OpenNextion/OpenNextion-SKU-ONX3248G035/Example Programs/ESP-IDF/05_wifi_test/README_en.md

# ESP32-S3 Wi-Fi Test Example

## Overview

This example demonstrates Wi-Fi scanning, connection, and status display on the ONX3248G035 development board (ESP32-S3). The UI is built with LVGL and the Wi-Fi logic is provided by the `wifi_manager` component.

## Purchase Links

- Product: [Open Nextion 3.5" Genius Series ESP32-S3 LCD Touchscreen Development Board](https://itead.cc/product/open-nextion-3-5-genius-series-esp32-s3-lcd-touchscreen-development-board/)

## Features

- **Wi-Fi scan**: scan nearby APs.
- **Wi-Fi connect**: select an SSID and connect (common WPA/WPA2).
- **Status UI**: show connection state and errors.

## Hardware Requirements

- **MCU**: ESP32-S3 Development Board
- **LCD**: 3.5-inch ST7796U SPI TFT LCD (320x480)
- **Touch**: CST826 I2C capacitive touch controller
- **IO Expander**: PCF8574 I2C IO expander

## Pin Connections (aligned with code)

| Function | ESP32-S3 Pin | Description |
| :--- | :--- | :--- |
| **I2C** | | |
| I2C SCL | GPIO_NUM_7 | I2C Clock |
| I2C SDA | GPIO_NUM_8 | I2C Data |
| **SPI (LCD)** | | |
| SPI SCLK | GPIO_NUM_5 | SPI Clock |
| SPI MOSI | GPIO_NUM_1 | SPI Data |
| LCD DC | GPIO_NUM_3 | LCD Data/Command |
| LCD CS | GPIO_NUM_2 | LCD Chip Select |
| **Other** | | |
| LCD BL | GPIO_NUM_6 | Backlight (PWM) |
| LCD RST | - | Controlled via PCF8574 |

## How to Use

1. **Connect hardware**: LCD + touch + board.
2. **Build and flash**.
3. **Provision Wi-Fi**: scan and select SSID on the screen, then enter password.

## Build and Flash

1. Set target:
   ```bash
   idf.py set-target esp32s3
   ```
2. Build:
   ```bash
   idf.py build
   ```
3. Flash and monitor:
   ```bash
   idf.py -p <PORT> flash monitor
   ```

## Notes

- Only 2.4 GHz Wi-Fi is supported on ESP32-S3.
- Use `menuconfig` to adjust Wi-Fi settings if needed.
