OpenNextion/OpenNextion-SKU-ONX3248G035/Example Programs/ESP-Arduino/02_music_test/build_opt.h

-DLV_CONF_SKIP
-DLV_USE_DEMO_MUSIC=1
-DLV_DEMO_MUSIC_SQUARE=0
-DLV_DEMO_MUSIC_LANDSCAPE=0
-DLV_DEMO_MUSIC_ROUND=0
-DLV_DEMO_MUSIC_LARGE=0
-DDEMO_MUSIC_AUTO_PLAY=0
-DLV_FONT_MONTSERRAT_16=1
-DLV_FONT_MONTSERRAT_22=1
-DLV_FONT_MONTSERRAT_32=1
