OpenNextion/OpenNextion-SKU-ONX3248G035/Example Programs/ESP-IDF/09_outofbox_demo/components/board/include/board_wifi.h

#ifndef  _BOARD_INCLUDE_BOARD_WIFI_H_
#define  _BOARD_INCLUDE_BOARD_WIFI_H_

#include "lvgl.h"


void vWifiSTAMode(void);

//返回 0X55为异常  否则为正常
signed char wifiGetFactoryRssi(void);


#endif /* _BOARD_INCLUDE_BOARD_WIFI_H_ */
